despina4/Proiect_TSC/Images/orbit_view_3D.png

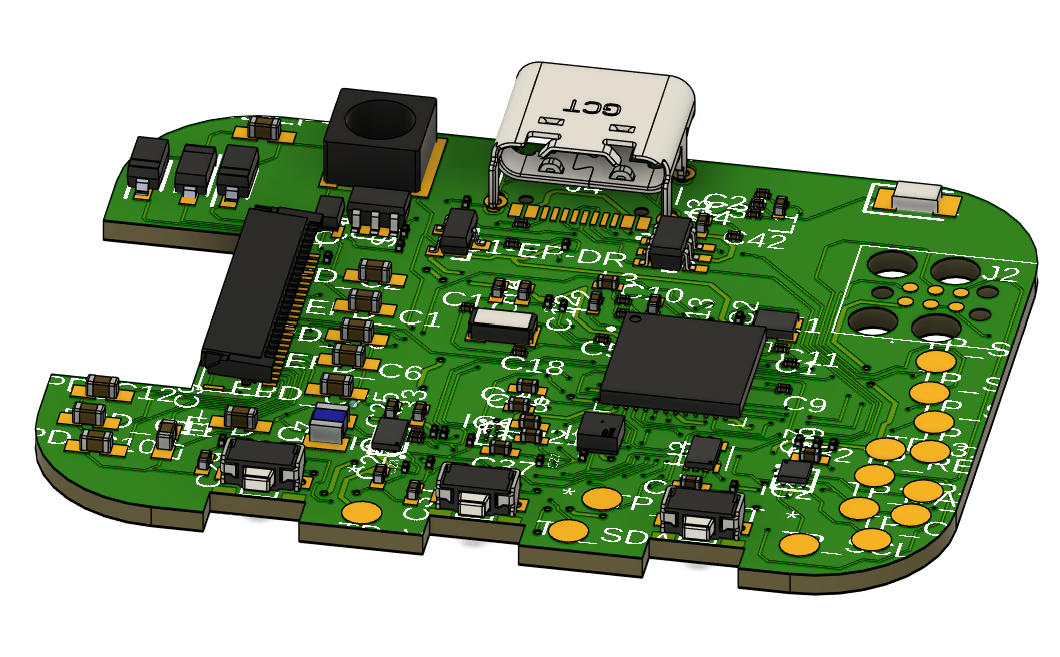
Images/orbit_view_3D.png
