despina4/Proiect_TSC/Images/PCB.png

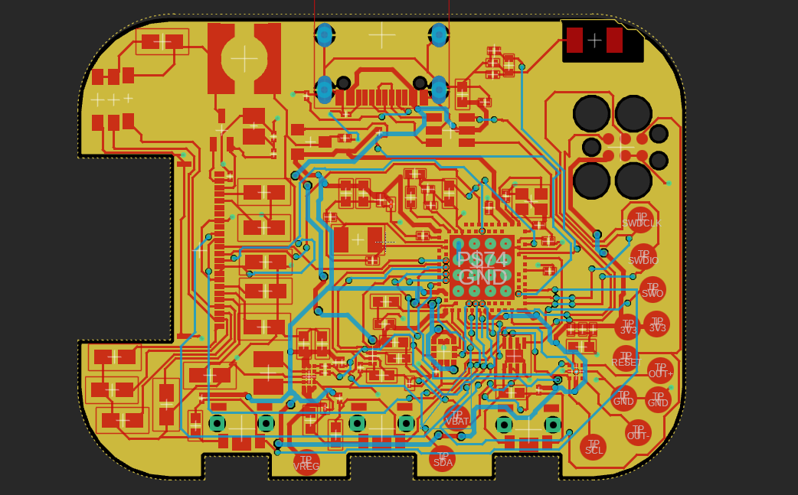
Images/PCB.png
