despina4/Proiect_TSC/Images/pcb_polygon.png

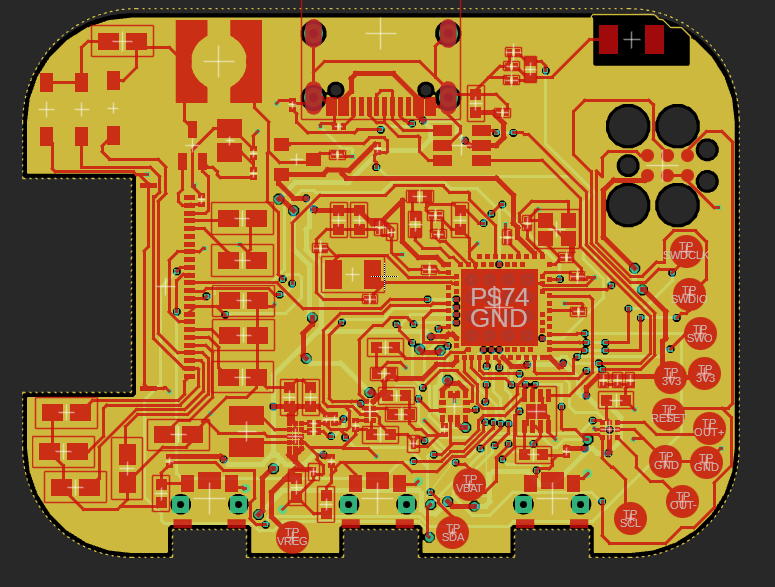
Images/pcb_polygon.png
